EchoDel/ToddlerTransducer/src/toddler_transducer/audio_file_manager.py

"""
Audio File Manager

Module which manages the audio files for the tool.
"""
import itertools
import json
from datetime import datetime
from pathlib import Path
from shutil import make_archive

from toddler_transducer.config import AUDIO_FILE_BASE_PATH, BACKUP_FILE_BASE_PATH
from toddler_transducer.metadata import load_metadata


def get_current_files() -> dict[str, str]:
    """Get current audio file paths keyed by track name.

    Returns:
        dict[str, str]: Mapping of track name to file name.
    """
    metadata = load_metadata()
    return {x['track_name']: x['file_name'] for x in metadata.values()}


def load_backup_metadata() -> dict[datetime, str]:
    """
    Load the backup metadata from disk.

    Returns:
        dict[datetime, str]: The backup metadata.
    """
    backup_list_file = BACKUP_FILE_BASE_PATH / 'backup_list.json'
    if backup_list_file.exists():
        with open(backup_list_file, 'r', encoding='UTF-8') as f:
            backup_list = json.load(f)
    else:
        backup_list = {}

    backup_list = {datetime.strptime(key, '%Y%m%d%H%M%S'): value for key, value in backup_list.items()}
    return backup_list


def save_backup_metadata(backup_list: dict[datetime, str]) -> None:
    """Save the backup metadata to disk.

    Args:
        backup_list (dict[datetime, str]): The backup metadata.
    """
    backup_list_file = BACKUP_FILE_BASE_PATH / 'backup_list.json'
    backup_list = {key.strftime('%Y%m%d%H%M%S'): value for key, value in backup_list.items()}

    with open(backup_list_file, 'w', encoding='UTF-8') as f:
        json.dump(backup_list, f)


def delete_old_backups(backups_to_delete: dict[datetime, str],
                       prior_backups: dict[datetime, str]) -> dict[datetime, str]:
    """Delete old backup ZIP files and return the updated backup dict.

    Args:
        backups_to_delete (dict[datetime, str]): The backups to delete.
        prior_backups (dict[datetime, str]): All prior backups.

    Returns:
        dict[datetime, str]: The updated backup metadata with old backups removed.
    """
    # Delete the old backups
    for backup_key, backup_path in backups_to_delete.items():
        prior_backups[backup_key] = None
        Path(backup_path).unlink()
    return prior_backups


def get_sorted_backup_item(location: int) -> dict[datetime, str]:
    """Get a single item from the sorted backup list by index.

    Positive index = oldest-first; negative index = newest-first.

    Args:
        location (int): The index of the item.

    Returns:
        dict[datetime, str]: The single value from the backup dict.
    """
    prior_backups = load_backup_metadata()
    if location < 0:
        sorted_dict = dict(sorted(prior_backups.items(), reverse=True))
        location = - location
    else:
        sorted_dict = dict(sorted(prior_backups.items()))
    # https://stackoverflow.com/questions/16976096/take-the-first-x-elements-of-a-dictionary-on-python
    return dict(itertools.islice(sorted_dict.items(), location))


def backup_audio_files() -> None:
    """Run the full backup process: zip audio files, register metadata, prune old backups."""
    prior_backups = load_backup_metadata()
    backup_time = datetime.now()
    backup_file = BACKUP_FILE_BASE_PATH / f'backup_{backup_time.strftime("%Y%m%d%H%M%S")}'
    make_archive(backup_file, 'zip', AUDIO_FILE_BASE_PATH)

    # Delete the old backups
    todays_backups = {key: value for key, value in prior_backups.items() if key.date() == datetime.now().date()}
    if len(todays_backups) > 1:
        prior_backups = delete_old_backups(todays_backups, prior_backups)

    # Save the backup
    prior_backups[backup_time] = str(backup_file.with_suffix('.zip'))

    # Delete the old backups
    if len(prior_backups) > 7:
        sorted_dict = dict(sorted(prior_backups.items()))
        items_to_remove = dict(itertools.islice(sorted_dict.items(), len(prior_backups) - 7))
        prior_backups = delete_old_backups(items_to_remove, prior_backups)

    save_backup_metadata(prior_backups)
