EchoDel/ToddlerTransducer/src/toddler_transducer/proxies/multithreading_proxy.py

"""
Multithreading proxy proxy

Provides a simple replacement for the Multithreading value when not multithreading
"""

class MultithreadingValueProxy:
    """
    Simple replacement for the Multithreading value when not multithreading
    """
    rfid_tag = 1000
    value = rfid_tag
